tdarlic/nimh_battery_charger/firmware/src/funconfig.h

#ifndef _FUNCONFIG_H
#define _FUNCONFIG_H

#define CH32V003           	1
// #define FUNCONF_USE_HSI		1
// #define FUNCONF_USE_PLL		1
#define FUNCONF_SYSTICK_USE_HCLK 1
#define FUNCONF_USE_DEBUGPRINTF 0
#define FUNCONF_USE_UARTPRINTF  1

#endif
